ojas-mediratta/ET55_Keyboard/images/bongo-cat-slam.jpeg

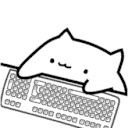
images/bongo-cat-slam.jpeg
