ojas-mediratta/ET55_Keyboard/et55_diagram/et55_diagram.kicad_sch

## KiCad design et55_diagram/et55_diagram.kicad_sch (2025-05-16)

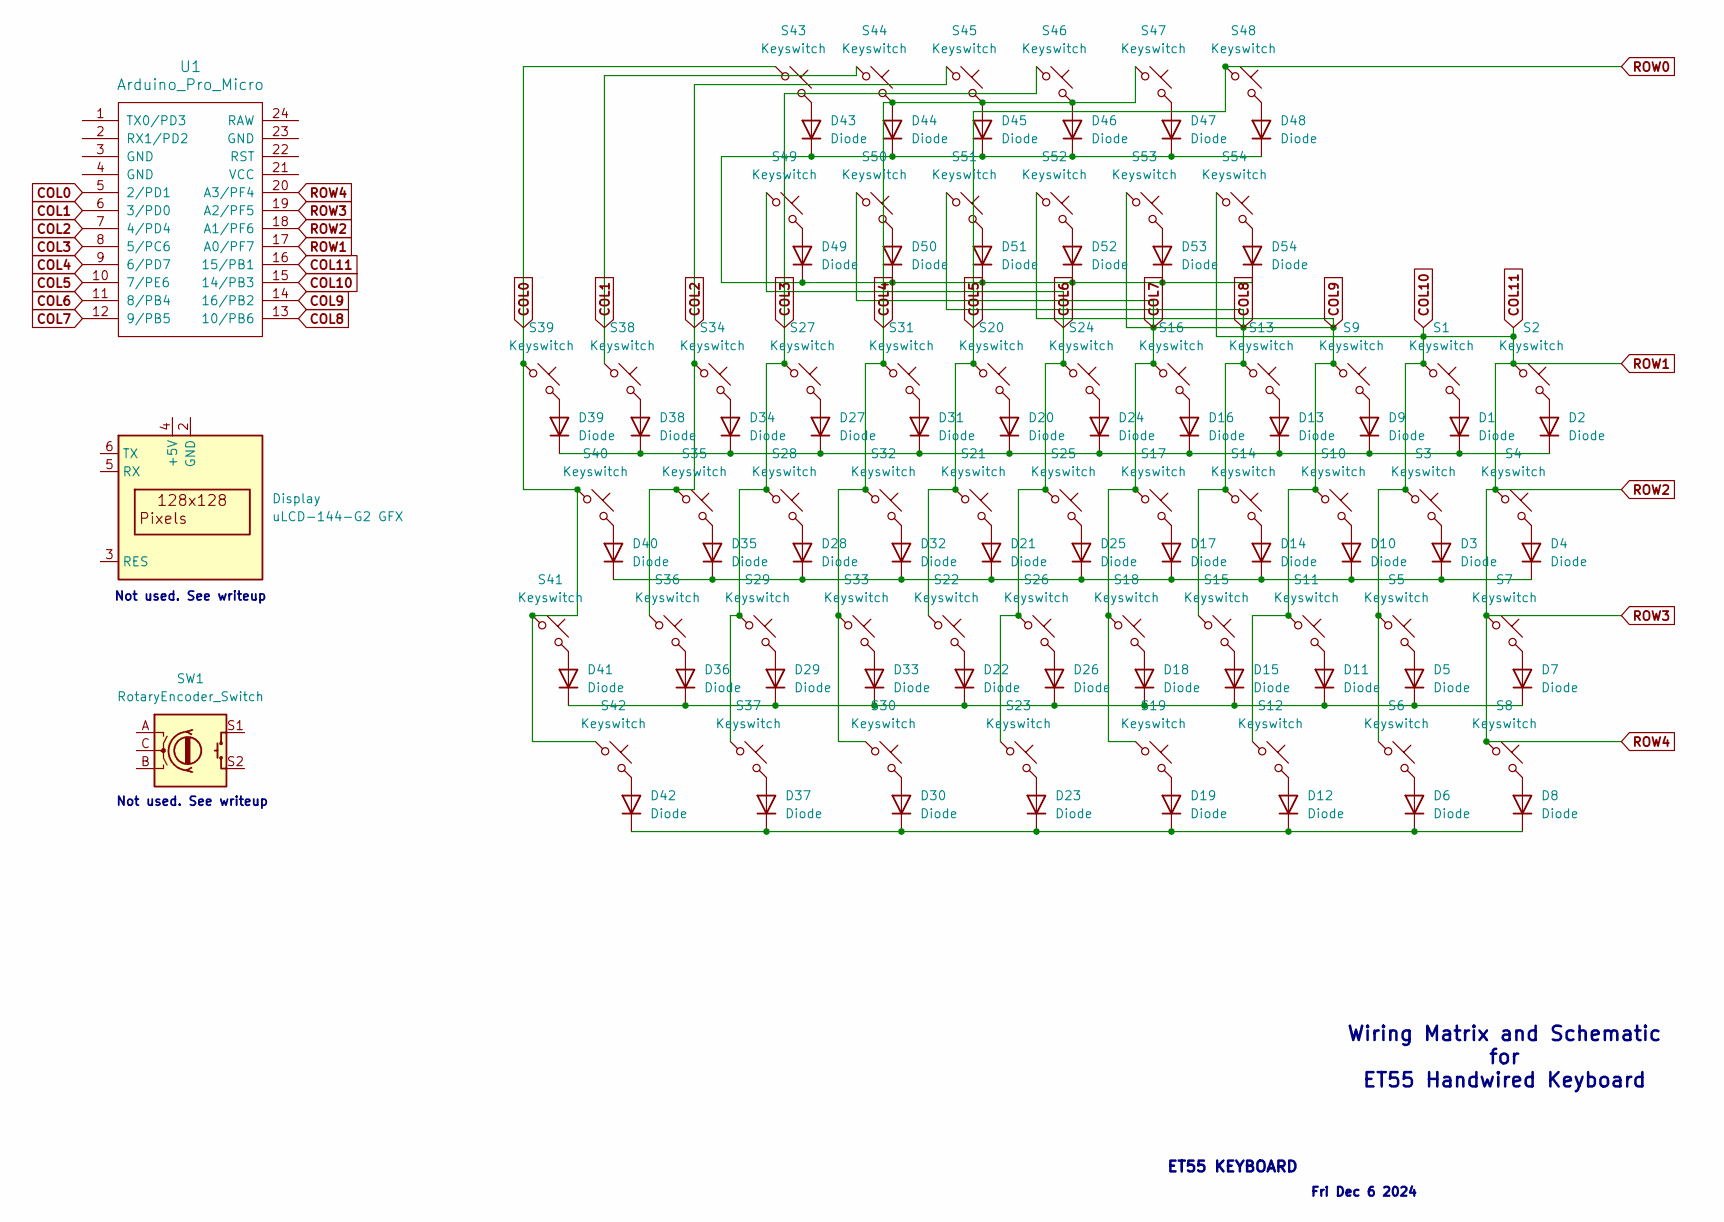
[picture p14: schematic et55_diagram.kicad_sch]

Parts:
D1, D2, D3, D4, D5, D6, D7, D8, D9, D10, D11, D12, D13, D14, D15, D16, D17, D18, D19, D20, D21, D22, D23, D24, D25, D26, D27, D28, D29, D30, D31, D32, D33, D34, D35, D36, D37, D38, D39, D40, D41, D42, D43, D44, D45, D46, D47, D48, D49, D50, D51, D52, D53, D54: Diode
Display: uLCD-144-G2 GFX; EA_T123X-I2C
S1, S2, S3, S4, S5, S6, S7, S8, S9, S10, S11, S12, S13, S14, S15, S16, S17, S18, S19, S20, S21, S22, S23, S24, S25, S26, S27, S28, S29, S30, S31, S32, S33, S34, S35, S36, S37, S38, S39, S40, S41, S42, S43, S44, S45, S46, S47, S48, S49, S50, S51, S52, S53, S54: Keyswitch
SW1: RotaryEncoder_Switch
U1: Arduino_Pro_Micro

Connections:
COL0: S39.1, S40.1, S41.1, S42.1, S43.1, U1.5 (2/PD1)
COL1: S38.1, S44.1, U1.6 (3/PD0)
COL2: S34.1, S35.1, S36.1, S45.1, U1.7 (4/PD4)
COL3: S27.1, S28.1, S29.1, S37.1, S46.1, U1.8 (5/PC6)
COL4: D44.2 (A), D45.2 (A), D46.2 (A), S30.1, S31.1, S32.1, S33.1, S44.2, S45.2, S46.2, S47.1, U1.9 (6/PD7)
COL5: S20.1, S21.1, S22.1, S48.1, U1.10 (7/PE6)
COL6: S23.1, S24.1, S25.1, S26.1, S49.1, U1.11 (8/PB4)
COL7: S9.1, S10.1, S11.1, S12.1, S13.1, S14.1, S15.1, S16.1, S17.1, S18.1, S19.1, S50.1, S51.1, S52.1, S53.1, U1.12 (9/PB5), U1.13 (10/PB6), U1.14 (16/PB2)
COL10: S1.1, S2.1, S3.1, S4.1, S5.1, S6.1, S7.1, S8.1, S54.1, U1.15 (14/PB3), U1.16 (15/PB1), U1.17 (A0/PF7), U1.18 (A1/PF6), U1.19 (A2/PF5), U1.20 (A3/PF4)
unnamed: D1.1 (K), D2.1 (K), D9.1 (K), D13.1 (K), D16.1 (K), D20.1 (K), D24.1 (K), D27.1 (K), D31.1 (K), D34.1 (K), D38.1 (K), D39.1 (K)
unnamed: D1.2 (A), S1.2
unnamed: D2.2 (A), S2.2
unnamed: D3.2 (A), S3.2
unnamed: D4.2 (A), S4.2
unnamed: D5.2 (A), S5.2
unnamed: D6.2 (A), S6.2
unnamed: D7.2 (A), S7.2
unnamed: D8.2 (A), S8.2
unnamed: D9.2 (A), S9.2
unnamed: D3.1 (K), D4.1 (K), D10.1 (K), D14.1 (K), D17.1 (K), D21.1 (K), D25.1 (K), D28.1 (K), D32.1 (K), D35.1 (K), D40.1 (K)
unnamed: D10.2 (A), S10.2
unnamed: D5.1 (K), D7.1 (K), D11.1 (K), D15.1 (K), D18.1 (K), D22.1 (K), D26.1 (K), D29.1 (K), D33.1 (K), D36.1 (K), D41.1 (K)
unnamed: D11.2 (A), S11.2
unnamed: D6.1 (K), D8.1 (K), D12.1 (K), D19.1 (K), D23.1 (K), D30.1 (K), D37.1 (K), D42.1 (K)
unnamed: D12.2 (A), S12.2
unnamed: D13.2 (A), S13.2
unnamed: D14.2 (A), S14.2
unnamed: D15.2 (A), S15.2
unnamed: D16.2 (A), S16.2
unnamed: D17.2 (A), S17.2
unnamed: D18.2 (A), S18.2
unnamed: D19.2 (A), S19.2
unnamed: D20.2 (A), S20.2
unnamed: D21.2 (A), S21.2
unnamed: D22.2 (A), S22.2
unnamed: D23.2 (A), S23.2
unnamed: D24.2 (A), S24.2
unnamed: D25.2 (A), S25.2
unnamed: D26.2 (A), S26.2
unnamed: D27.2 (A), S27.2
unnamed: D28.2 (A), S28.2
unnamed: D29.2 (A), S29.2
unnamed: D30.2 (A), S30.2
unnamed: D31.2 (A), S31.2
unnamed: D32.2 (A), S32.2
unnamed: D33.2 (A), S33.2
unnamed: D34.2 (A), S34.2
unnamed: D35.2 (A), S35.2
unnamed: D36.2 (A), S36.2
unnamed: D37.2 (A), S37.2
unnamed: D38.2 (A), S38.2
unnamed: D39.2 (A), S39.2
unnamed: D40.2 (A), S40.2
unnamed: D41.2 (A), S41.2
unnamed: D42.2 (A), S42.2
unnamed: D43.1 (K), D44.1 (K), D45.1 (K), D46.1 (K), D47.1 (K), D48.1 (K), D49.1 (K), D50.1 (K), D51.1 (K), D52.1 (K), D53.1 (K), D54.1 (K)
unnamed: D43.2 (A), S43.2
unnamed: D47.2 (A), S47.2
unnamed: D48.2 (A), S48.2
unnamed: D49.2 (A), S49.2
unnamed: D50.2 (A), S50.2
unnamed: D51.2 (A), S51.2
unnamed: D52.2 (A), S52.2
unnamed: D53.2 (A), S53.2
unnamed: D54.2 (A), S54.2

Notes on the sheet:
Not used. See writeup
ET55 KEYBOARD
Wiring Matrix and Schematic for ET55 Handwired Keyboard
Fri Dec 6 2024
